Bemeier/bmek/pcb/kicad/projects/BMEK_Hotswap/BMEK_Hotswap.kicad_sch

## KiCad design pcb/kicad/projects/BMEK_Hotswap/BMEK_Hotswap.kicad_sch (2021-01-31)

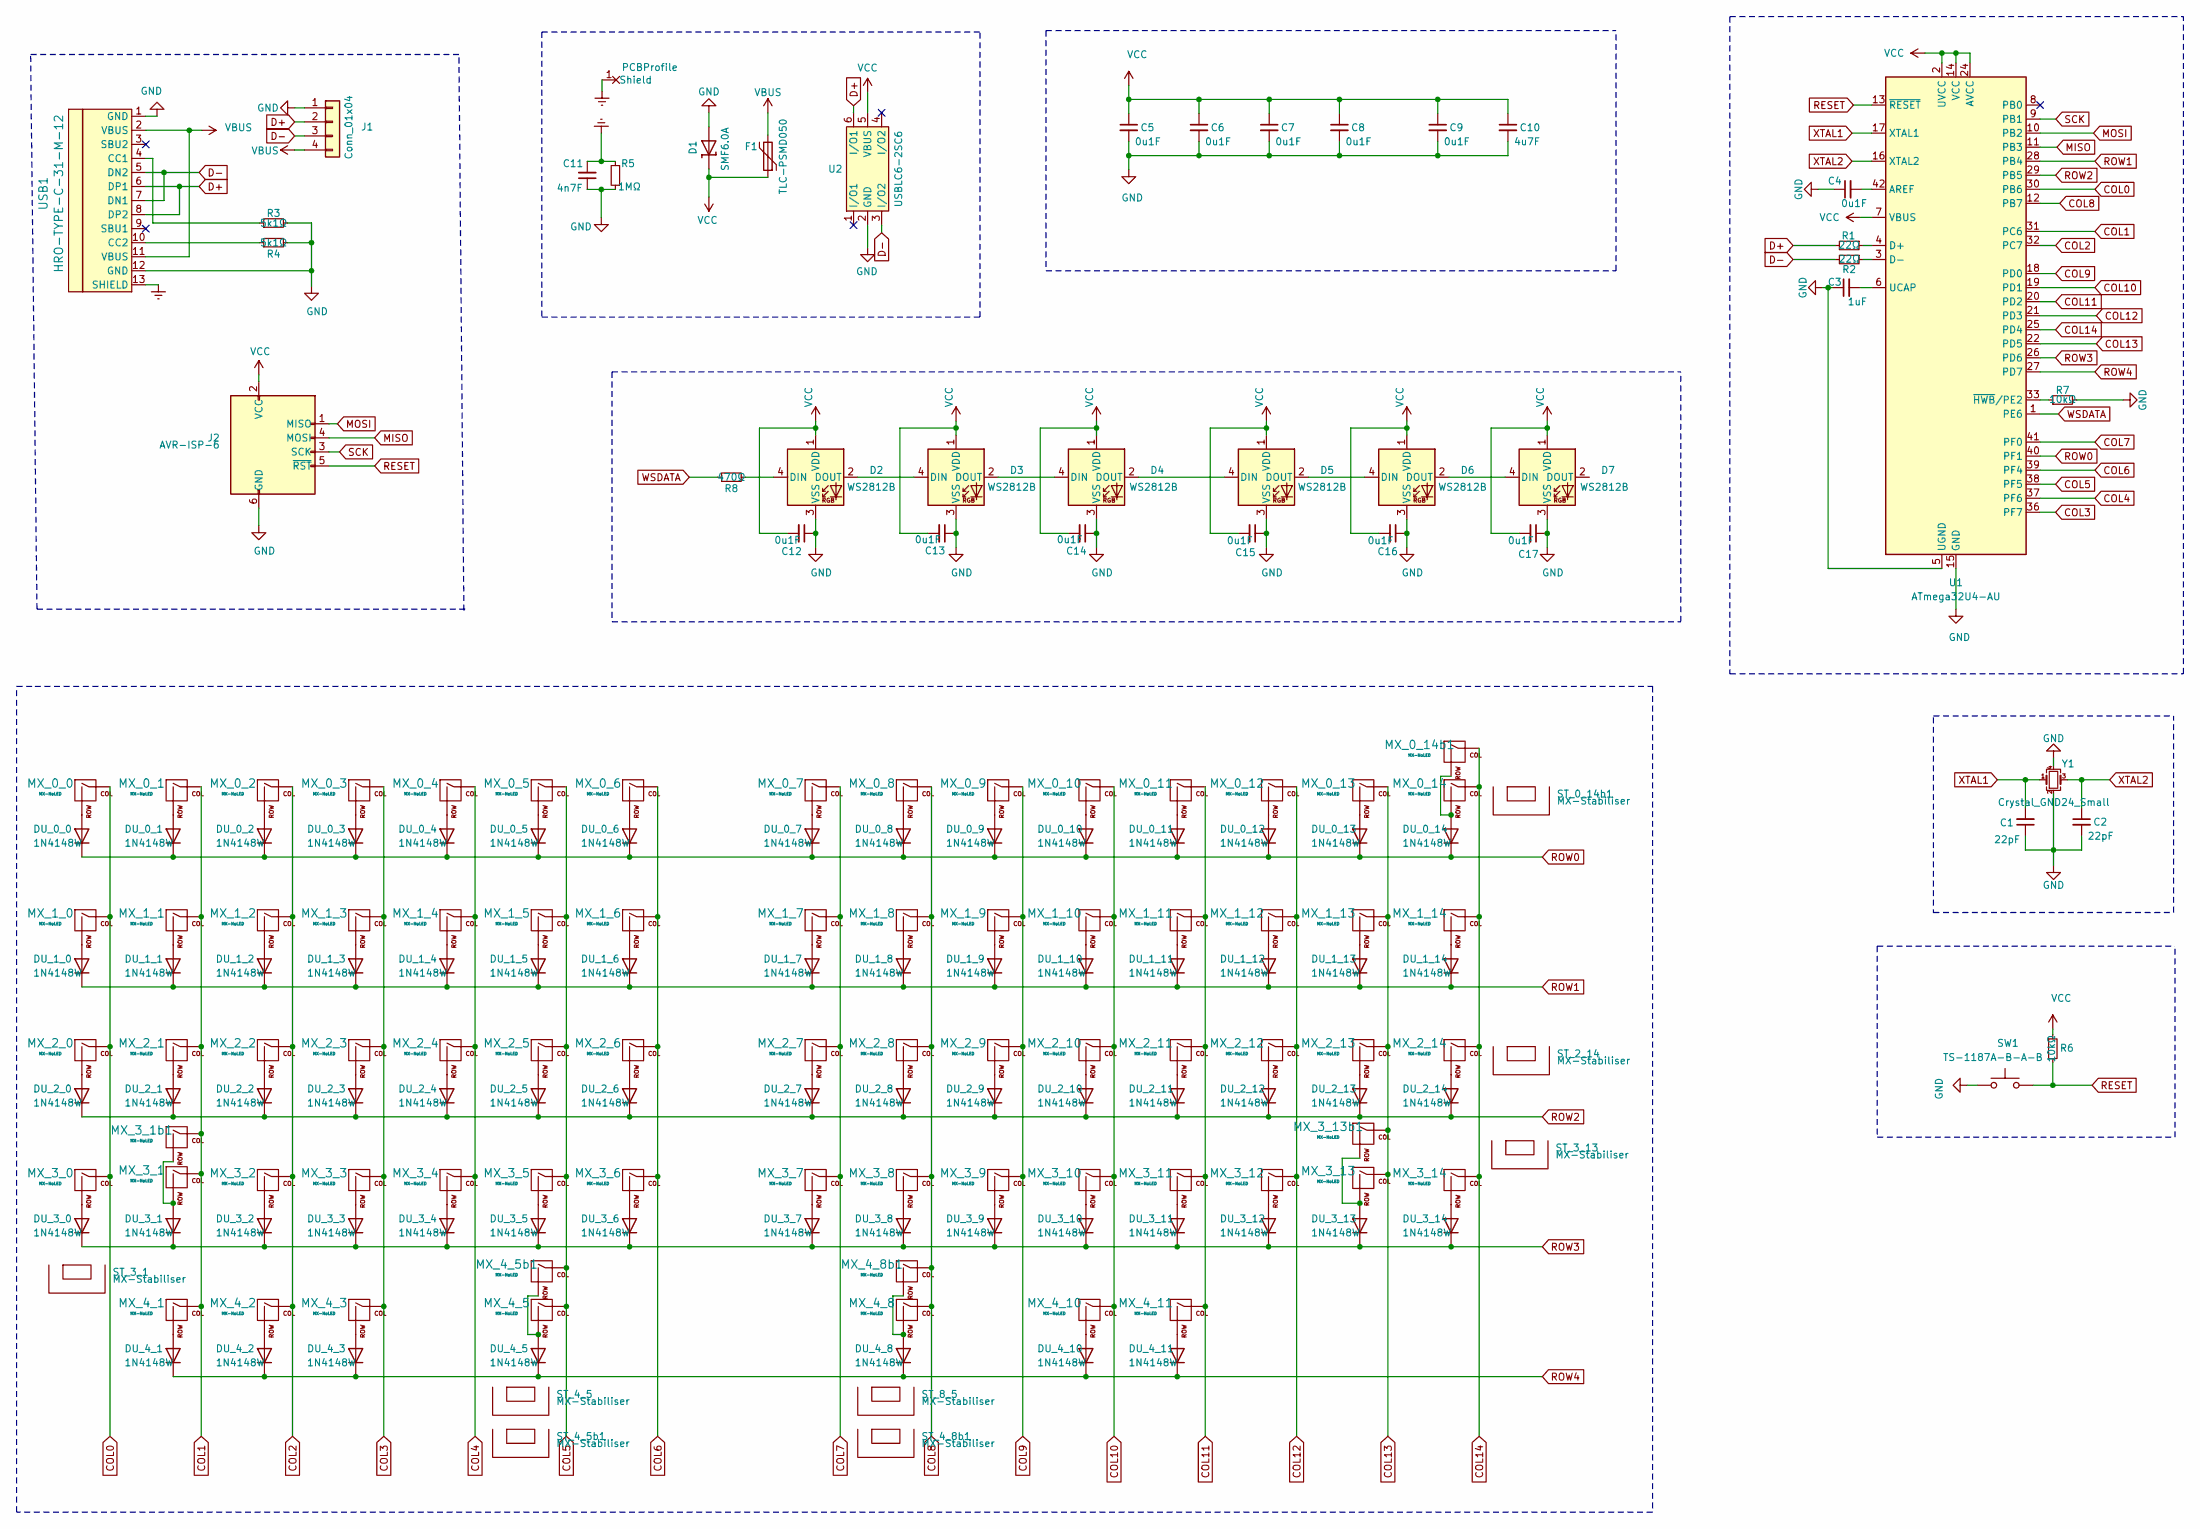
[picture p25: schematic BMEK_Hotswap.kicad_sch]

Parts:
C1, C2: 22pF; C_0603_1608Metric; LCSC C1653
C3: 1uF; C_0603_1608Metric; LCSC C15849
C4, C5, C6, C7, C8, C9, C12, C13, C14, C15, C16, C17: 0u1F; C_0603_1608Metric; LCSC C14663
C10: 4u7F; C_0603_1608Metric; LCSC C19666
C11: 4n7F; C_0603_1608Metric; LCSC C159797
D1: SMF6.0A; D_SOD-123; LCSC C123790
D2, D3, D4, D5, D6, D7: WS2812B; LED_WS2812B_PLCC4_5.0x5.0mm_P3.2mm; LCSC C114586
DU_0_0, DU_0_1, DU_0_2, DU_0_3, DU_0_4, DU_0_5, DU_0_6, DU_0_7, DU_0_8, DU_0_9, DU_0_10, DU_0_11, DU_0_12, DU_0_13, DU_0_14, DU_1_0, DU_1_1, DU_1_2, DU_1_3, DU_1_4, DU_1_5, DU_1_6, DU_1_7, DU_1_8, DU_1_9, DU_1_10, DU_1_11, DU_1_12, DU_1_13, DU_1_14, DU_2_0, DU_2_1, DU_2_2, DU_2_3, DU_2_4, DU_2_5, DU_2_6, DU_2_7, DU_2_8, DU_2_9, DU_2_10, DU_2_11, DU_2_12, DU_2_13, DU_2_14, DU_3_0, DU_3_1, DU_3_2, DU_3_3, DU_3_4, DU_3_5, DU_3_6, DU_3_7, DU_3_8, DU_3_9, DU_3_10, DU_3_11, DU_3_12, DU_3_13, DU_3_14, DU_4_1, DU_4_2, DU_4_3, DU_4_5, DU_4_8, DU_4_10, DU_4_11: 1N4148W; D_SOD-123; LCSC C81598
F1: TLC-PSMD050; Fuse_0805_2012Metric; LCSC C261942
J1: Conn_01x04; PinHeader_1x04_P2.54mm_Vertical
J2: AVR-ISP-6; PinHeader_2x03_P2.54mm_Vertical
MX_0_0, MX_0_1, MX_0_2, MX_0_3, MX_0_4, MX_0_5, MX_0_6, MX_0_7, MX_0_8, MX_0_9, MX_0_10, MX_0_11, MX_0_12, MX_0_13, MX_0_14, MX_0_14b1, MX_1_0, MX_1_1, MX_1_2, MX_1_3, MX_1_4, MX_1_5, MX_1_6, MX_1_7, MX_1_8, MX_1_9, MX_1_10, MX_1_11, MX_1_12, MX_1_13, MX_1_14, MX_2_0, MX_2_1, MX_2_2, MX_2_3, MX_2_4, MX_2_5, MX_2_6, MX_2_7, MX_2_8, MX_2_9, MX_2_10, MX_2_11, MX_2_12, MX_2_13, MX_2_14, MX_3_0, MX_3_1, MX_3_1b1, MX_3_2, MX_3_3, MX_3_4, MX_3_5, MX_3_6, MX_3_7, MX_3_8, MX_3_9, MX_3_10, MX_3_11, MX_3_12, MX_3_13, MX_3_13b1, MX_3_14, MX_4_1, MX_4_2, MX_4_3, MX_4_5, MX_4_5b1, MX_4_8, MX_4_8b1, MX_4_10, MX_4_11: MX-NoLED; MX-1U-Hotswap
R1, R2: 22Ω; R_0603_1608Metric; LCSC C23345
R3, R4: 5k1Ω; R_0603_1608Metric; LCSC C23186
R5: 1MΩ; R_0603_1608Metric; LCSC C22935
R6, R7: 10kΩ; R_0603_1608Metric; LCSC C25804
R8: 470Ω; R_0603_1608Metric; LCSC C23179
ST_0_14b1, ST_2_14, ST_3_1, ST_3_13, ST_4_5, ST_4_5b1, ST_4_8b1, ST_8_5: MX-Stabiliser; MX-Stabiliser-2.25U
SW1: TS-1187A-B-A-B; LCSC C318884
U1: ATmega32U4-AU; TQFP-44_10x10mm_P0.8mm; LCSC C44854
U2: USBLC6-2SC6; SOT95P280X145-6N; LCSC C7519
USB1: HRO-TYPE-C-31-M-12; HRO-TYPE-C-31-M-12-HandSoldering; LCSC C165948
V1: PCBProfile; PCBProfile_NO_Switches
Y1: Crystal_GND24_Small; SMD3225; LCSC C13738

Connections:
COL0: MX_0_0.1 (COL), MX_1_0.1 (COL), MX_2_0.1 (COL), MX_3_0.1 (COL), U1.30 (PB6)
COL1: MX_0_1.1 (COL), MX_1_1.1 (COL), MX_2_1.1 (COL), MX_3_1.1 (COL), MX_3_1b1.1 (COL), MX_4_1.1 (COL), U1.31 (PC6)
COL2: MX_0_2.1 (COL), MX_1_2.1 (COL), MX_2_2.1 (COL), MX_3_2.1 (COL), MX_4_2.1 (COL), U1.32 (PC7)
COL3: MX_0_3.1 (COL), MX_1_3.1 (COL), MX_2_3.1 (COL), MX_3_3.1 (COL), MX_4_3.1 (COL), U1.36 (PF7)
COL4: MX_0_4.1 (COL), MX_1_4.1 (COL), MX_2_4.1 (COL), MX_3_4.1 (COL), U1.37 (PF6)
COL5: MX_0_5.1 (COL), MX_1_5.1 (COL), MX_2_5.1 (COL), MX_3_5.1 (COL), MX_4_5.1 (COL), MX_4_5b1.1 (COL), U1.38 (PF5)
COL6: MX_0_6.1 (COL), MX_1_6.1 (COL), MX_2_6.1 (COL), MX_3_6.1 (COL), U1.39 (PF4)
COL7: MX_0_7.1 (COL), MX_1_7.1 (COL), MX_2_7.1 (COL), MX_3_7.1 (COL), U1.41 (PF0)
COL8: MX_0_8.1 (COL), MX_1_8.1 (COL), MX_2_8.1 (COL), MX_3_8.1 (COL), MX_4_8.1 (COL), MX_4_8b1.1 (COL), U1.12 (PB7)
COL9: MX_0_9.1 (COL), MX_1_9.1 (COL), MX_2_9.1 (COL), MX_3_9.1 (COL), U1.18 (PD0)
COL10: MX_0_10.1 (COL), MX_1_10.1 (COL), MX_2_10.1 (COL), MX_3_10.1 (COL), MX_4_10.1 (COL), U1.19 (PD1)
COL11: MX_0_11.1 (COL), MX_1_11.1 (COL), MX_2_11.1 (COL), MX_3_11.1 (COL), MX_4_11.1 (COL), U1.20 (PD2)
COL12: MX_0_12.1 (COL), MX_1_12.1 (COL), MX_2_12.1 (COL), MX_3_12.1 (COL), U1.21 (PD3)
COL13: MX_0_13.1 (COL), MX_1_13.1 (COL), MX_2_13.1 (COL), MX_3_13.1 (COL), MX_3_13b1.1 (COL), U1.22 (PD5)
COL14: MX_0_14.1 (COL), MX_0_14b1.1 (COL), MX_1_14.1 (COL), MX_2_14.1 (COL), MX_3_14.1 (COL), U1.25 (PD4)
D+: J1.2, R1.2, U2.6 (I/O1), USB1.6 (DP1), USB1.8 (DP2)
D-: J1.3, R2.2, U2.3 (I/O2), USB1.5 (DN2), USB1.7 (DN1)
Earth: C11.2, R5.2, USB1.13 (SHIELD), V1.1
GND: C1.1, C2.2, C3.1, C4.1, C5.2, C6.2, C7.2, C8.2, C9.2, C10.2, C11.1, C12.1, C13.1, C14.1, C15.1, C16.1, C17.1, D1.2 (A), D2.3 (VSS), D3.3 (VSS), D4.3 (VSS), D5.3 (VSS), D6.3 (VSS), D7.3 (VSS), J1.1, J2.6 (GND), R3.2, R4.2, R5.1, R7.2, SW1.1, U1.5 (UGND), U1.15 (GND), U1.23 (GND), U1.35 (GND), U1.43 (GND), U2.2 (GND), USB1.1 (GND), USB1.12 (GND), Y1.2, Y1.4
MISO: J2.4 (MOSI), U1.11 (PB3)
MOSI: J2.1 (MISO), U1.10 (PB2)
unnamed: C3.2, U1.6 (UCAP)
unnamed: C4.2, U1.42 (AREF)
unnamed: D2.2 (DOUT), D3.4 (DIN)
unnamed: D2.4 (DIN), R8.2
unnamed: D3.2 (DOUT), D4.4 (DIN)
unnamed: D4.2 (DOUT), D5.4 (DIN)
unnamed: D5.2 (DOUT), D6.4 (DIN)
unnamed: D6.2 (DOUT), D7.4 (DIN)
unnamed: DU_0_0.2 (A), MX_0_0.2 (ROW)
unnamed: DU_0_1.2 (A), MX_0_1.2 (ROW)
unnamed: DU_0_2.2 (A), MX_0_2.2 (ROW)
unnamed: DU_0_3.2 (A), MX_0_3.2 (ROW)
unnamed: DU_0_4.2 (A), MX_0_4.2 (ROW)
unnamed: DU_0_5.2 (A), MX_0_5.2 (ROW)
unnamed: DU_0_6.2 (A), MX_0_6.2 (ROW)
unnamed: DU_0_7.2 (A), MX_0_7.2 (ROW)
unnamed: DU_0_8.2 (A), MX_0_8.2 (ROW)
unnamed: DU_0_9.2 (A), MX_0_9.2 (ROW)
unnamed: DU_0_10.2 (A), MX_0_10.2 (ROW)
unnamed: DU_0_11.2 (A), MX_0_11.2 (ROW)
unnamed: DU_0_12.2 (A), MX_0_12.2 (ROW)
unnamed: DU_0_13.2 (A), MX_0_13.2 (ROW)
unnamed: DU_0_14.2 (A), MX_0_14.2 (ROW), MX_0_14b1.2 (ROW)
unnamed: DU_1_0.2 (A), MX_1_0.2 (ROW)
unnamed: DU_1_1.2 (A), MX_1_1.2 (ROW)
unnamed: DU_1_2.2 (A), MX_1_2.2 (ROW)
unnamed: DU_1_3.2 (A), MX_1_3.2 (ROW)
unnamed: DU_1_4.2 (A), MX_1_4.2 (ROW)
unnamed: DU_1_5.2 (A), MX_1_5.2 (ROW)
unnamed: DU_1_6.2 (A), MX_1_6.2 (ROW)
unnamed: DU_1_7.2 (A), MX_1_7.2 (ROW)
unnamed: DU_1_8.2 (A), MX_1_8.2 (ROW)
unnamed: DU_1_9.2 (A), MX_1_9.2 (ROW)
unnamed: DU_1_10.2 (A), MX_1_10.2 (ROW)
unnamed: DU_1_11.2 (A), MX_1_11.2 (ROW)
unnamed: DU_1_12.2 (A), MX_1_12.2 (ROW)
unnamed: DU_1_13.2 (A), MX_1_13.2 (ROW)
unnamed: DU_1_14.2 (A), MX_1_14.2 (ROW)
unnamed: DU_2_0.2 (A), MX_2_0.2 (ROW)
unnamed: DU_2_1.2 (A), MX_2_1.2 (ROW)
unnamed: DU_2_2.2 (A), MX_2_2.2 (ROW)
unnamed: DU_2_3.2 (A), MX_2_3.2 (ROW)
unnamed: DU_2_4.2 (A), MX_2_4.2 (ROW)
unnamed: DU_2_5.2 (A), MX_2_5.2 (ROW)
unnamed: DU_2_6.2 (A), MX_2_6.2 (ROW)
unnamed: DU_2_7.2 (A), MX_2_7.2 (ROW)
unnamed: DU_2_8.2 (A), MX_2_8.2 (ROW)
unnamed: DU_2_9.2 (A), MX_2_9.2 (ROW)
unnamed: DU_2_10.2 (A), MX_2_10.2 (ROW)
unnamed: DU_2_11.2 (A), MX_2_11.2 (ROW)
unnamed: DU_2_12.2 (A), MX_2_12.2 (ROW)
unnamed: DU_2_13.2 (A), MX_2_13.2 (ROW)
unnamed: DU_2_14.2 (A), MX_2_14.2 (ROW)
unnamed: DU_3_0.2 (A), MX_3_0.2 (ROW)
unnamed: DU_3_1.2 (A), MX_3_1.2 (ROW), MX_3_1b1.2 (ROW)
unnamed: DU_3_2.2 (A), MX_3_2.2 (ROW)
unnamed: DU_3_3.2 (A), MX_3_3.2 (ROW)
unnamed: DU_3_4.2 (A), MX_3_4.2 (ROW)
unnamed: DU_3_5.2 (A), MX_3_5.2 (ROW)
unnamed: DU_3_6.2 (A), MX_3_6.2 (ROW)
unnamed: DU_3_7.2 (A), MX_3_7.2 (ROW)
unnamed: DU_3_8.2 (A), MX_3_8.2 (ROW)
unnamed: DU_3_9.2 (A), MX_3_9.2 (ROW)
unnamed: DU_3_10.2 (A), MX_3_10.2 (ROW)
unnamed: DU_3_11.2 (A), MX_3_11.2 (ROW)
unnamed: DU_3_12.2 (A), MX_3_12.2 (ROW)
unnamed: DU_3_13.2 (A), MX_3_13.2 (ROW), MX_3_13b1.2 (ROW)
unnamed: DU_3_14.2 (A), MX_3_14.2 (ROW)
unnamed: DU_4_1.2 (A), MX_4_1.2 (ROW)
unnamed: DU_4_2.2 (A), MX_4_2.2 (ROW)
unnamed: DU_4_3.2 (A), MX_4_3.2 (ROW)
unnamed: DU_4_5.2 (A), MX_4_5.2 (ROW), MX_4_5b1.2 (ROW)
unnamed: DU_4_8.2 (A), MX_4_8.2 (ROW), MX_4_8b1.2 (ROW)
unnamed: DU_4_10.2 (A), MX_4_10.2 (ROW)
unnamed: DU_4_11.2 (A), MX_4_11.2 (ROW)
unnamed: R1.1, U1.4 (D+)
unnamed: R2.1, U1.3 (D-)
unnamed: R3.1, USB1.4 (CC1)
unnamed: R4.1, USB1.10 (CC2)
unnamed: R7.1, U1.33 (~HWB~/PE2)
RESET: J2.5 (~RST), R6.2, SW1.2, U1.13 (~RESET)
ROW0: DU_0_0.1 (K), DU_0_1.1 (K), DU_0_2.1 (K), DU_0_3.1 (K), DU_0_4.1 (K), DU_0_5.1 (K), DU_0_6.1 (K), DU_0_7.1 (K), DU_0_8.1 (K), DU_0_9.1 (K), DU_0_10.1 (K), DU_0_11.1 (K), DU_0_12.1 (K), DU_0_13.1 (K), DU_0_14.1 (K), U1.40 (PF1)
ROW1: DU_1_0.1 (K), DU_1_1.1 (K), DU_1_2.1 (K), DU_1_3.1 (K), DU_1_4.1 (K), DU_1_5.1 (K), DU_1_6.1 (K), DU_1_7.1 (K), DU_1_8.1 (K), DU_1_9.1 (K), DU_1_10.1 (K), DU_1_11.1 (K), DU_1_12.1 (K), DU_1_13.1 (K), DU_1_14.1 (K), U1.28 (PB4)
ROW2: DU_2_0.1 (K), DU_2_1.1 (K), DU_2_2.1 (K), DU_2_3.1 (K), DU_2_4.1 (K), DU_2_5.1 (K), DU_2_6.1 (K), DU_2_7.1 (K), DU_2_8.1 (K), DU_2_9.1 (K), DU_2_10.1 (K), DU_2_11.1 (K), DU_2_12.1 (K), DU_2_13.1 (K), DU_2_14.1 (K), U1.29 (PB5)
ROW3: DU_3_0.1 (K), DU_3_1.1 (K), DU_3_2.1 (K), DU_3_3.1 (K), DU_3_4.1 (K), DU_3_5.1 (K), DU_3_6.1 (K), DU_3_7.1 (K), DU_3_8.1 (K), DU_3_9.1 (K), DU_3_10.1 (K), DU_3_11.1 (K), DU_3_12.1 (K), DU_3_13.1 (K), DU_3_14.1 (K), U1.26 (PD6)
ROW4: DU_4_1.1 (K), DU_4_2.1 (K), DU_4_3.1 (K), DU_4_5.1 (K), DU_4_8.1 (K), DU_4_10.1 (K), DU_4_11.1 (K), U1.27 (PD7)
SCK: J2.3 (SCK), U1.9 (PB1)
VBUS: F1.2, J1.4, USB1.2 (VBUS), USB1.11 (VBUS)
VCC: C5.1, C6.1, C7.1, C8.1, C9.1, C10.1, C12.2, C13.2, C14.2, C15.2, C16.2, C17.2, D1.1 (K), D2.1 (VDD), D3.1 (VDD), D4.1 (VDD), D5.1 (VDD), D6.1 (VDD), D7.1 (VDD), F1.1, J2.2 (VCC), R6.1, U1.2 (UVCC), U1.7 (VBUS), U1.14 (VCC), U1.24 (AVCC), U1.34 (VCC), U1.44 (AVCC), U2.5 (VBUS)
WSDATA: R8.1, U1.1 (PE6)
XTAL1: C1.2, U1.17 (XTAL1), Y1.1
XTAL2: C2.1, U1.16 (XTAL2), Y1.3
